ozkan/skywatch/Hardware/skywatch.kicad_sch

## KiCad design Hardware/skywatch.kicad_sch (2024-01-29)

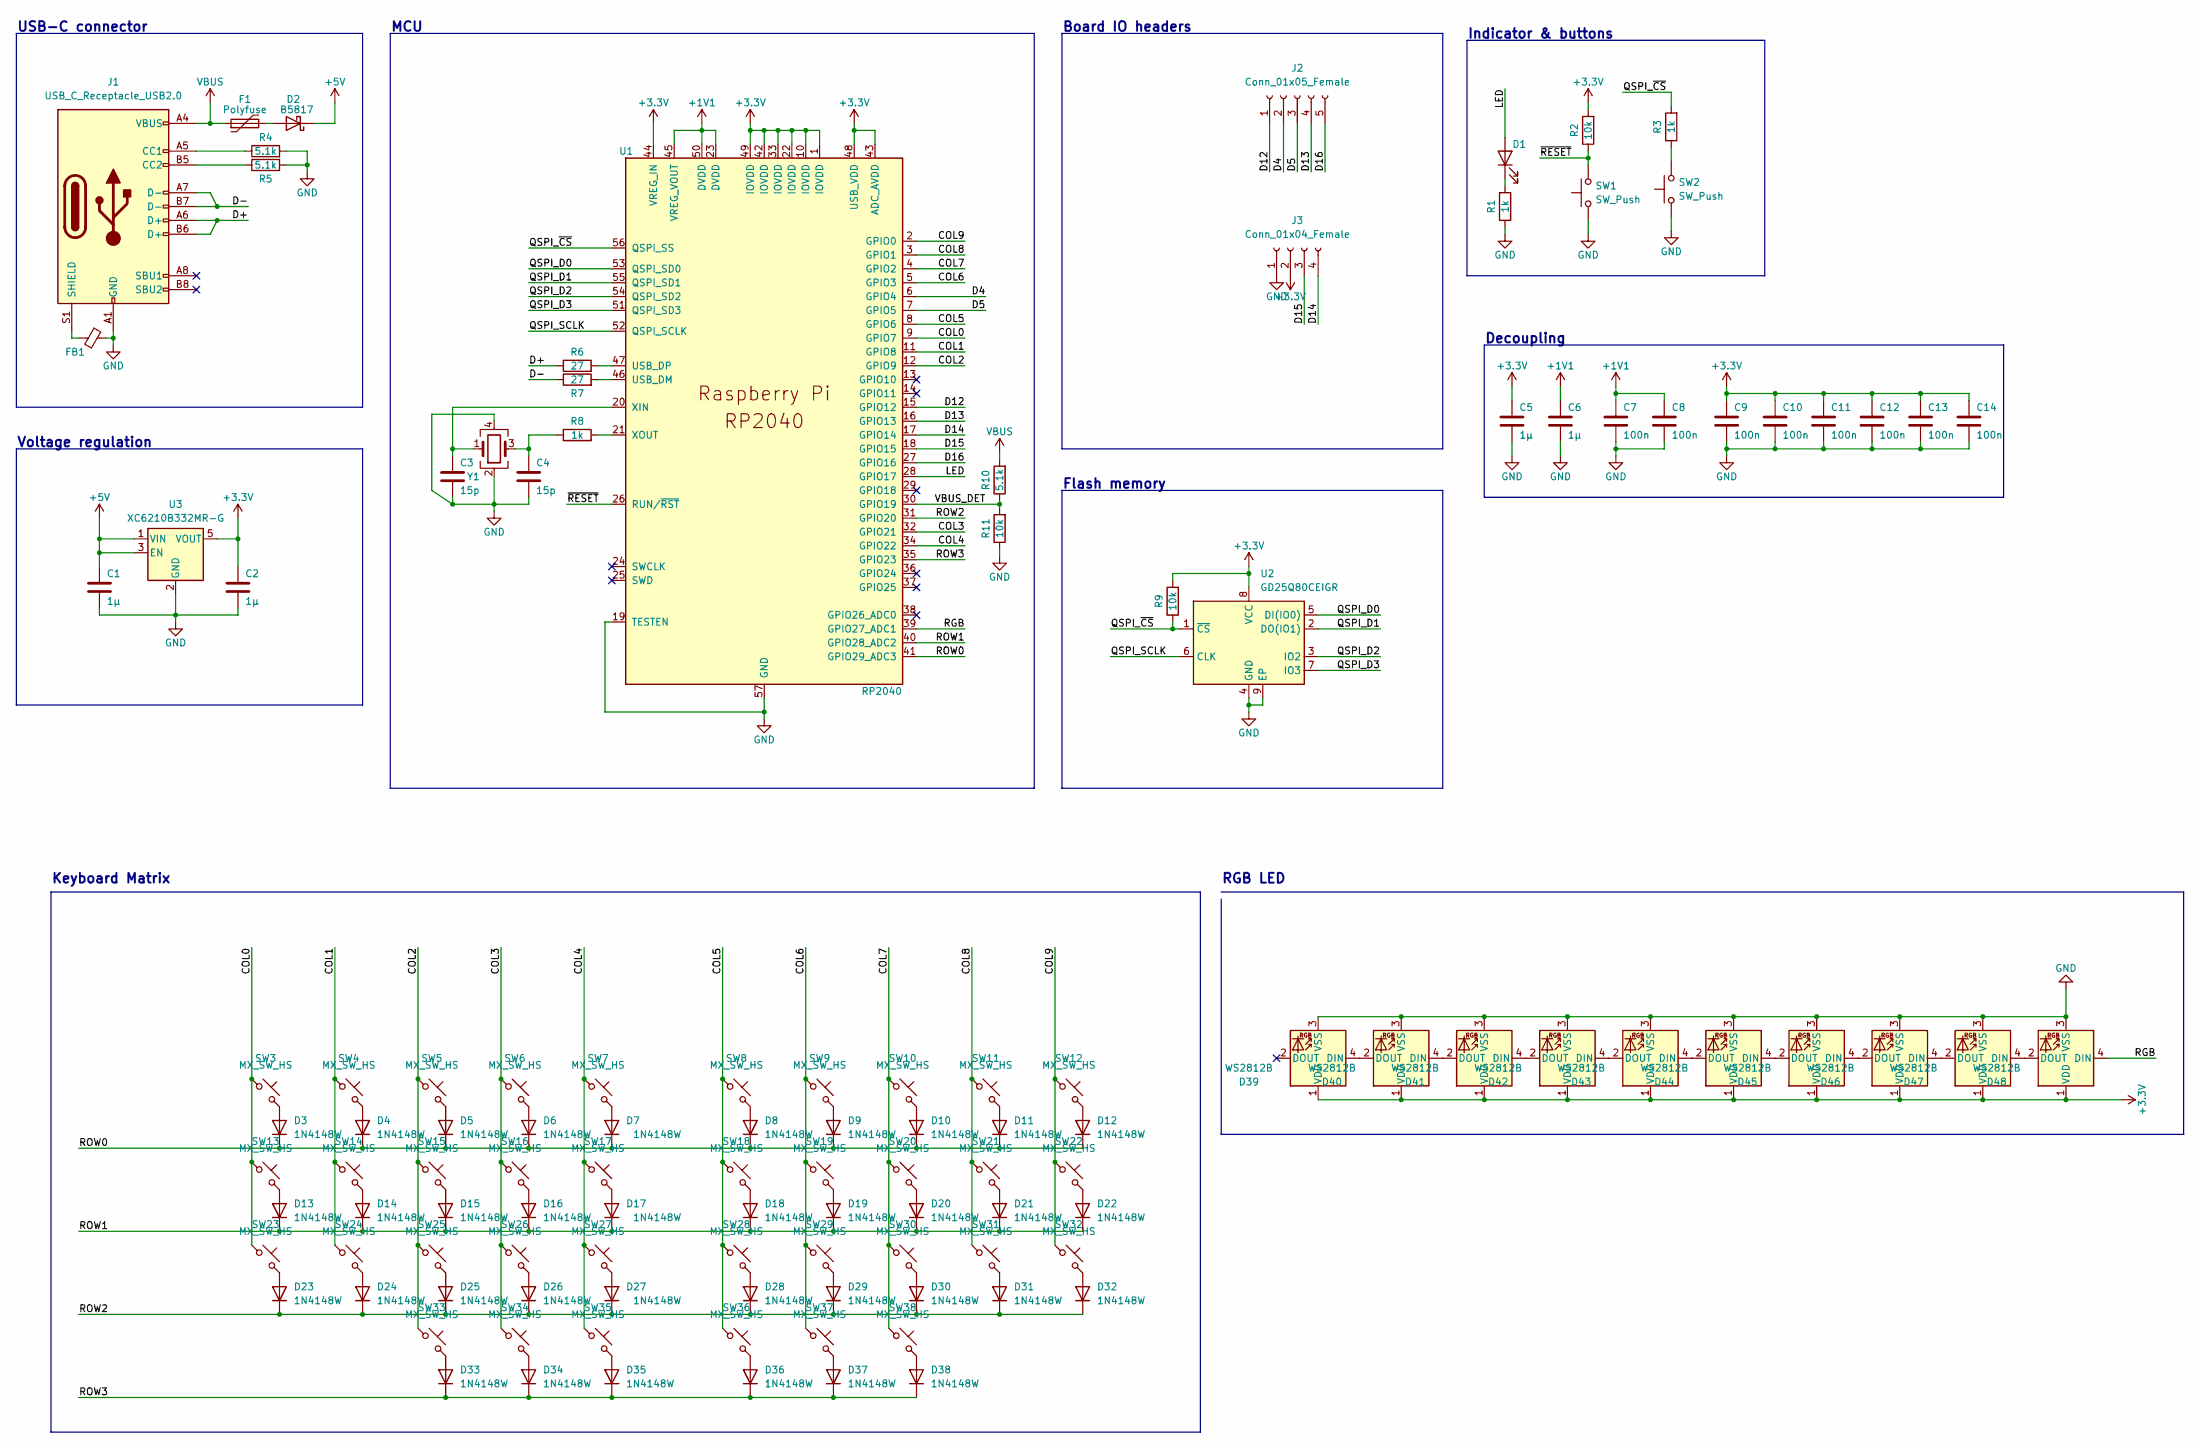
[picture p9: schematic skywatch.kicad_sch]

Parts:
C1, C2: 1µ; C_0603_1608Metric; LCSC C19666
C3, C4: 15p; C_0402_1005Metric; LCSC C1548
C5, C6: 1µ; C_0402_1005Metric; LCSC C52923
C7, C8, C9, C10, C11, C12, C13, C14: 100n; C_0402_1005Metric; LCSC C1525
D1: LED; LED_0402_1005Metric; LCSC C130719
D2: B5817; D_SOD-323; LCSC C123899
D3, D4, D5, D6, D7, D8, D9, D10, D11, D12, D13, D14, D15, D16, D17, D18, D19, D20, D21, D22, D23, D24, D25, D26, D27, D28, D29, D30, D31, D32, D33, D34, D35, D36, D37, D38: 1N4148W; D_SOD-323; LCSC C2843305
D39, D40, D41, D42, D43, D44, D45, D46, D47, D48: WS2812B; LED_WS2812B_PLCC4_5.0x5.0mm_P3.2mm; LCSC C2843785
F1: Polyfuse; Fuse_0603_1608Metric; LCSC C69679
FB1: FerriteBead_Small; L_0603_1608Metric; LCSC C98288
J1: USB_C_Receptacle_USB2.0; USB_C_Receptacle_HRO_TYPE-C-31-M-13B; LCSC C2848619
J2: Conn_01x05_Female; PinHeader_1x05_P2.54mm_Vertical
J3: Conn_01x04_Female; PinHeader_1x04_P2.54mm_Vertical
R1, R3, R8: 1k; R_0402_1005Metric; LCSC C11702
R2, R9, R11: 10k; R_0402_1005Metric; LCSC C25744
R4, R5, R10: 5.1k; R_0402_1005Metric; LCSC C25905
R6, R7: 27; R_0402_1005Metric; LCSC C25100
SW1, SW2: SW_Push; SW_SPST_CK_KXT3; LCSC C319433
SW3, SW4, SW5, SW6, SW7, SW8, SW9, SW10, SW11, SW12, SW13, SW14, SW15, SW16, SW17, SW18, SW19, SW20, SW21, SW22, SW23, SW24, SW25, SW26, SW27, SW28, SW29, SW30, SW31, SW32, SW33, SW34, SW35, SW36, SW37, SW38: MX_SW_HS; MX_TH_HS_1U
U1: RP2040; QFN-56-1EP_7x7mm_P0.4mm_EP3.2x3.2mm; LCSC C2040
U2: GD25Q80CEIGR; USON-8-1EP_3x2mm_P0.5mm_EP0.25x1.65mm; LCSC C395484
U3: XC6210B332MR-G; SOT-23-5; LCSC C82942
Y1: Crystal_GND24; Crystal_SMD_2520-4Pin_2.5x2.0mm; LCSC C2149204

Connections:
+1V1: C6.1, C7.1, C8.1, U1.23 (DVDD), U1.45 (VREG_VOUT), U1.50 (DVDD)
+3.3V: C2.1, C5.1, C9.1, C10.1, C11.1, C12.1, C13.1, C14.1, D39.1 (VDD), D40.1 (VDD), D41.1 (VDD), D42.1 (VDD), D43.1 (VDD), D44.1 (VDD), D45.1 (VDD), D46.1 (VDD), D47.1 (VDD), D48.1 (VDD), J3.2, R2.2, R9.2, U1.1 (IOVDD), U1.10 (IOVDD), U1.22 (IOVDD), U1.33 (IOVDD), U1.42 (IOVDD), U1.43 (ADC_AVDD), U1.44 (VREG_IN), U1.48 (USB_VDD), U1.49 (IOVDD), U2.8 (VCC), U3.5 (VOUT)
+5V: C1.1, D2.1 (K), U3.1 (VIN), U3.3 (EN)
COL0: SW3.1, SW13.1, SW23.1, U1.9 (GPIO7)
COL1: SW4.1, SW14.1, SW24.1, U1.11 (GPIO8)
COL2: SW5.1, SW15.1, SW25.1, SW33.1, U1.12 (GPIO9)
COL3: SW6.1, SW16.1, SW26.1, SW34.1, U1.32 (GPIO21)
COL4: SW7.1, SW17.1, SW27.1, SW35.1, U1.34 (GPIO22)
COL5: SW8.1, SW18.1, SW28.1, SW36.1, U1.8 (GPIO6)
COL6: SW9.1, SW19.1, SW29.1, SW37.1, U1.5 (GPIO3)
COL7: SW10.1, SW20.1, SW30.1, SW38.1, U1.4 (GPIO2)
COL8: SW11.1, SW21.1, SW31.1, U1.3 (GPIO1)
COL9: SW12.1, SW22.1, SW32.1, U1.2 (GPIO0)
D4: J2.2, U1.6 (GPIO4)
D5: J2.3, U1.7 (GPIO5)
D12: J2.1, U1.15 (GPIO12)
D13: J2.4, U1.16 (GPIO13)
D14: J3.4, U1.17 (GPIO14)
D15: J3.3, U1.18 (GPIO15)
D16: J2.5, U1.27 (GPIO16)
D+: J1.A6 (D+), J1.B6 (D+), R6.1
D-: J1.A7 (D-), J1.B7 (D-), R7.1
GND: C1.2, C2.2, C3.2, C4.2, C5.2, C6.2, C7.2, C8.2, C9.2, C10.2, C11.2, C12.2, C13.2, C14.2, D39.3 (VSS), D40.3 (VSS), D41.3 (VSS), D42.3 (VSS), D43.3 (VSS), D44.3 (VSS), D45.3 (VSS), D46.3 (VSS), D47.3 (VSS), D48.3 (VSS), FB1.1, J1.A1 (GND), J1.A12 (GND), J1.B1 (GND), J1.B12 (GND), J3.1, R1.1, R4.2, R5.2, R11.1, SW1.1, SW2.1, U1.19 (TESTEN), U1.57 (GND), U2.4 (GND), U2.9 (EP), U3.2 (GND), Y1.2, Y1.4
LED: D1.2 (A), U1.28 (GPIO17)
unnamed: C3.1, U1.20 (XIN), Y1.1
unnamed: C4.1, R8.1, Y1.3
unnamed: D1.1 (K), R1.2
unnamed: D2.2 (A), F1.2
unnamed: D3.2 (A), SW3.2
unnamed: D4.2 (A), SW4.2
unnamed: D5.2 (A), SW5.2
unnamed: D6.2 (A), SW6.2
unnamed: D7.2 (A), SW7.2
unnamed: D8.2 (A), SW8.2
unnamed: D9.2 (A), SW9.2
unnamed: D10.2 (A), SW10.2
unnamed: D11.2 (A), SW11.2
unnamed: D12.2 (A), SW12.2
unnamed: D13.2 (A), SW13.2
unnamed: D14.2 (A), SW14.2
unnamed: D15.2 (A), SW15.2
unnamed: D16.2 (A), SW16.2
unnamed: D17.2 (A), SW17.2
unnamed: D18.2 (A), SW18.2
unnamed: D19.2 (A), SW19.2
unnamed: D20.2 (A), SW20.2
unnamed: D21.2 (A), SW21.2
unnamed: D22.2 (A), SW22.2
unnamed: D23.2 (A), SW23.2
unnamed: D24.2 (A), SW24.2
unnamed: D25.2 (A), SW25.2
unnamed: D26.2 (A), SW26.2
unnamed: D27.2 (A), SW27.2
unnamed: D28.2 (A), SW28.2
unnamed: D29.2 (A), SW29.2
unnamed: D30.2 (A), SW30.2
unnamed: D31.2 (A), SW31.2
unnamed: D32.2 (A), SW32.2
unnamed: D33.2 (A), SW33.2
unnamed: D34.2 (A), SW34.2
unnamed: D35.2 (A), SW35.2
unnamed: D36.2 (A), SW36.2
unnamed: D37.2 (A), SW37.2
unnamed: D38.2 (A), SW38.2
unnamed: D39.4 (DIN), D40.2 (DOUT)
unnamed: D40.4 (DIN), D41.2 (DOUT)
unnamed: D41.4 (DIN), D42.2 (DOUT)
unnamed: D42.4 (DIN), D43.2 (DOUT)
unnamed: D43.4 (DIN), D44.2 (DOUT)
unnamed: D44.4 (DIN), D45.2 (DOUT)
unnamed: D45.4 (DIN), D46.2 (DOUT)
unnamed: D46.4 (DIN), D47.2 (DOUT)
unnamed: D47.4 (DIN), D48.2 (DOUT)
unnamed: FB1.2, J1.S1 (SHIELD)
unnamed: J1.A5 (CC1), R4.1
unnamed: J1.B5 (CC2), R5.1
unnamed: R3.1, SW2.2
unnamed: R6.2, U1.47 (USB_DP)
unnamed: R7.2, U1.46 (USB_DM)
unnamed: R8.2, U1.21 (XOUT)
QSPI_D0: U1.53 (QSPI_SD0), U2.5 (DI(IO0))
QSPI_D1: U1.55 (QSPI_SD1), U2.2 (DO(IO1))
QSPI_D2: U1.54 (QSPI_SD2), U2.3 (IO2)
QSPI_D3: U1.51 (QSPI_SD3), U2.7 (IO3)
QSPI_SCLK: U1.52 (QSPI_SCLK), U2.6 (CLK)
QSPI_~CS: R3.2, R9.1, U1.56 (QSPI_SS), U2.1 (~CS)
RGB: D48.4 (DIN), U1.39 (GPIO27_ADC1)
ROW0: D3.1 (K), D4.1 (K), D5.1 (K), D6.1 (K), D7.1 (K), D8.1 (K), D9.1 (K), D10.1 (K), D11.1 (K), D12.1 (K), U1.41 (GPIO29_ADC3)
ROW1: D13.1 (K), D14.1 (K), D15.1 (K), D16.1 (K), D17.1 (K), D18.1 (K), D19.1 (K), D20.1 (K), D21.1 (K), D22.1 (K), U1.40 (GPIO28_ADC2)
ROW2: D23.1 (K), D24.1 (K), D25.1 (K), D26.1 (K), D27.1 (K), D28.1 (K), D29.1 (K), D30.1 (K), D31.1 (K), D32.1 (K), U1.31 (GPIO20)
ROW3: D33.1 (K), D34.1 (K), D35.1 (K), D36.1 (K), D37.1 (K), D38.1 (K), U1.35 (GPIO23)
VBUS: F1.1, J1.A4 (VBUS), J1.A9 (VBUS), J1.B4 (VBUS), J1.B9 (VBUS), R10.2
VBUS_DET: R10.1, R11.2, U1.30 (GPIO19)
~RESET: R2.1, SW1.2, U1.26 (RUN/~RST)

Notes on the sheet:
Decoupling
Board IO headers
USB-C connector
Indicator & buttons
Voltage regulation
MCU
RGB LED
Flash memory
Keyboard Matrix
